jpt13653903/FUI-Audio-DAC/LT-Spice/Primary Power.asc

C1: cap; 470µ; Rser=1
C2: cap; 4µ7
C3: cap; 470µ
D1: diode; RFN5TF8S
D2: diode; RFN5TF8S
D3: diode; RFN5TF8S
D4: diode; RFN5TF8S
D5: zener; PTZ15B
D6: diode; RFN5TF8S
D7: diode; RFN5TF8S
I1: current; 45m
I2: current; 1A
R1: res; 10e
V1: voltage; SINE(0 325 50)
Named nets: 0
.tran 0 1.1 1
2x ISO721 (14 mA each)
2x Regulator (8 mA each)
1x IR2181 (1 mA)
