jpt13653903/FUI-Audio-DAC/Quartus/USB Amplifier/Audio/NoiseShaper.v

//==============================================================================
// Copyright (C) John-Philip Taylor
// jpt13653903@gmail.com
//
// This file is part of a library
//
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
module NoiseShaper #(
 parameter InputN  = 24,
 parameter OutputN =  8,
 parameter N       =  4  // Order of the noise shaper
)(
 input  Reset,
 input  Clk,
 input  Clk_Ena,

 input      [InputN -1:0]Input,
 output reg [OutputN-1:0]Output
);
//------------------------------------------------------------------------------

wire [(InputN+1)        :0]t1;
reg  [(InputN-1)        :0]t2;
reg  [(InputN-OutputN+N):0]t3[2*N+1:0];
wire [(InputN+1)        :0]t4;
//------------------------------------------------------------------------------
 
assign t1 = t4 + Input;
//------------------------------------------------------------------------------

reg tReset;

always @(posedge Clk) begin
 tReset <= Reset;

 if(tReset) begin
  t2     <= 0;
  Output <= 0;
   
 end else if(Clk_Ena) begin
  if     (t1[InputN+1]) t2 <= 0;
  else if(t1[InputN  ]) t2 <= {InputN{1'b1}};
  else                  t2 <= t1[InputN-1:0];
 end
 
 Output <= t2[InputN-1:InputN-OutputN];
end
//------------------------------------------------------------------------------

always @* begin 
 t3[0] <= {{(N+1){1'b0}}, t2[InputN-OutputN-1:0]};
end
//------------------------------------------------------------------------------

generate
genvar g;
 for(g = 0; g < N; g = g + 1) begin: NS_Blocks
  always @* begin
   t3[2*g+2] <= t3[2*g] - t3[2*g+1];
  end
   
  always @(posedge Clk) begin
   if     (tReset ) t3[2*g+1] <= 0;
   else if(Clk_Ena) t3[2*g+1] <= t3[2*g];
  end
 end 
endgenerate
//------------------------------------------------------------------------------

always @* begin
 t3[2*N+1] <= t3[0] - t3[2*N];
end
//------------------------------------------------------------------------------
 
assign t4 = {{(OutputN-N+1){t3[2*N+1][InputN-OutputN+N]}}, t3[2*N+1]};
//------------------------------------------------------------------------------

endmodule
//------------------------------------------------------------------------------
